Xinyuan-LilyGO/T-Halow/docs/EMC Authentication/泰芯AH模组-TX-AH-Rx00P 日本MIC证书&报告_20231007103027/MIC-RL-Certificate_230905005_219-239312.pdf

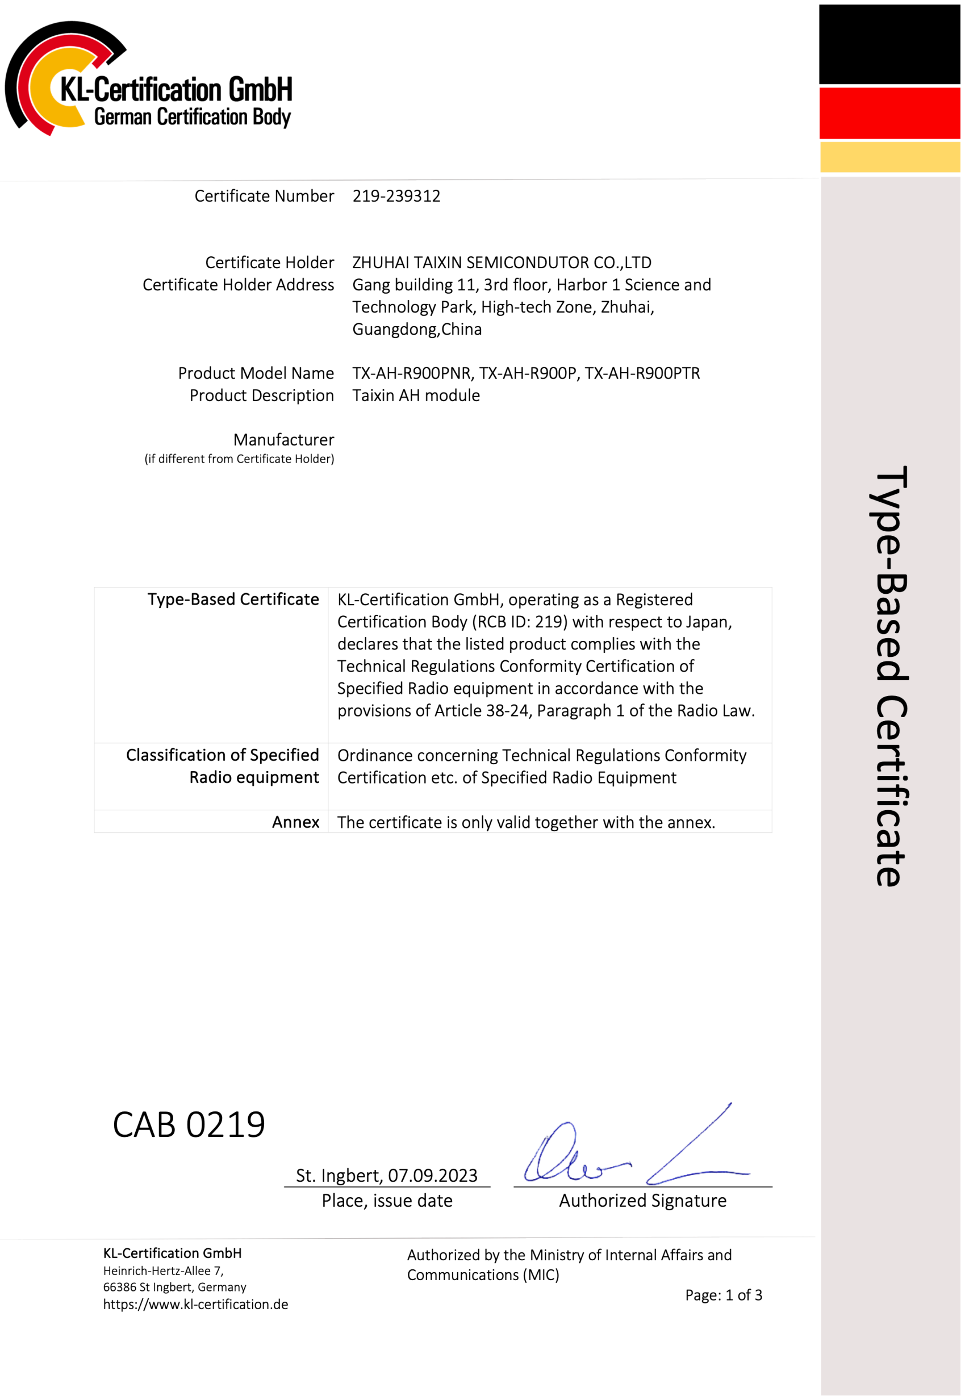
[picture p26: page 1]
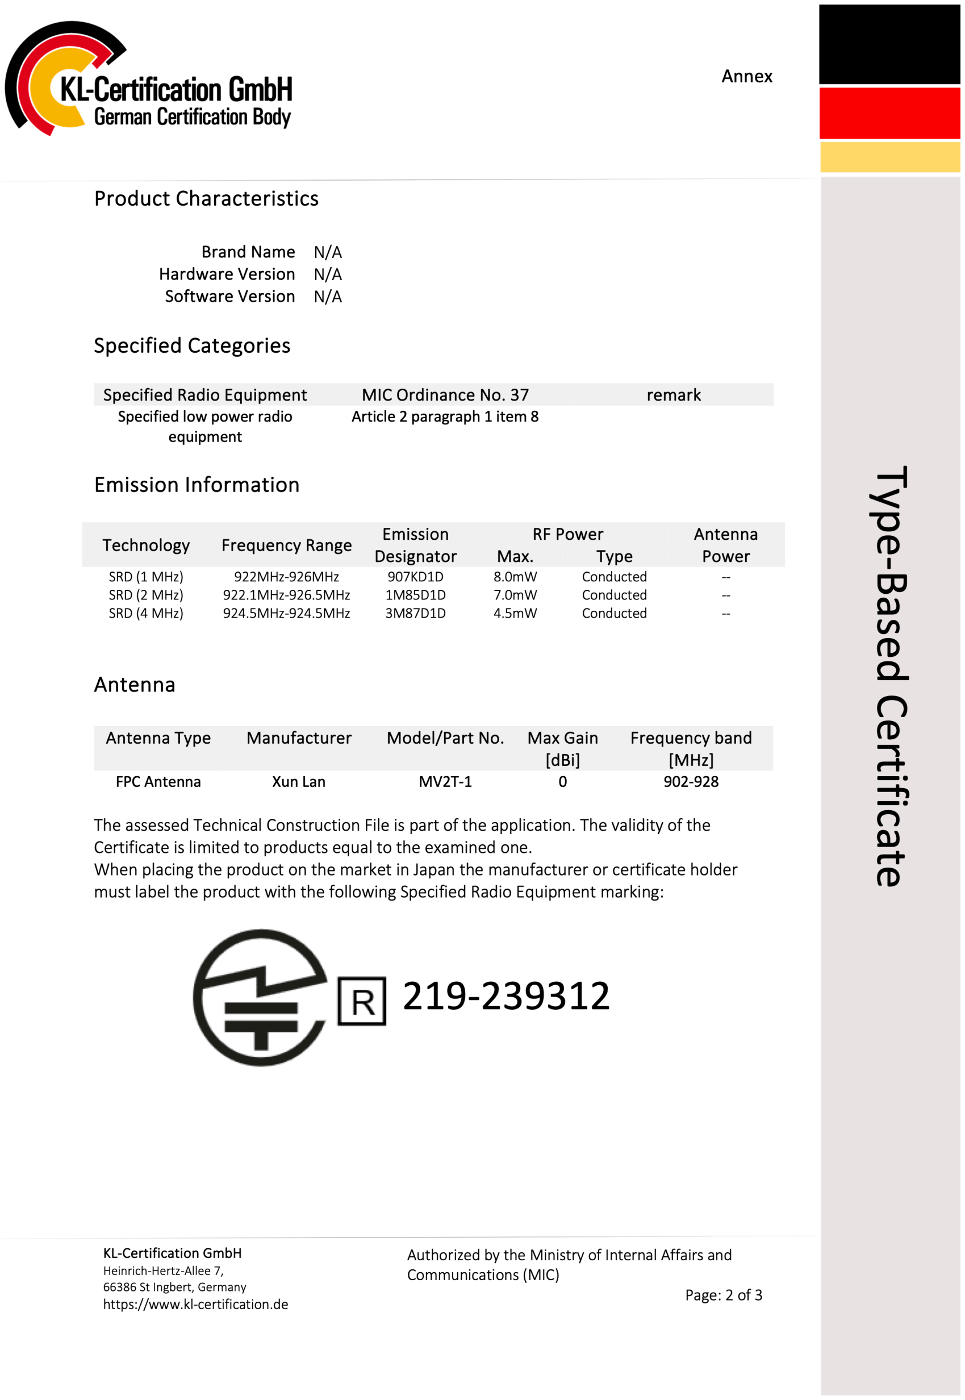
[picture p27: page 2]
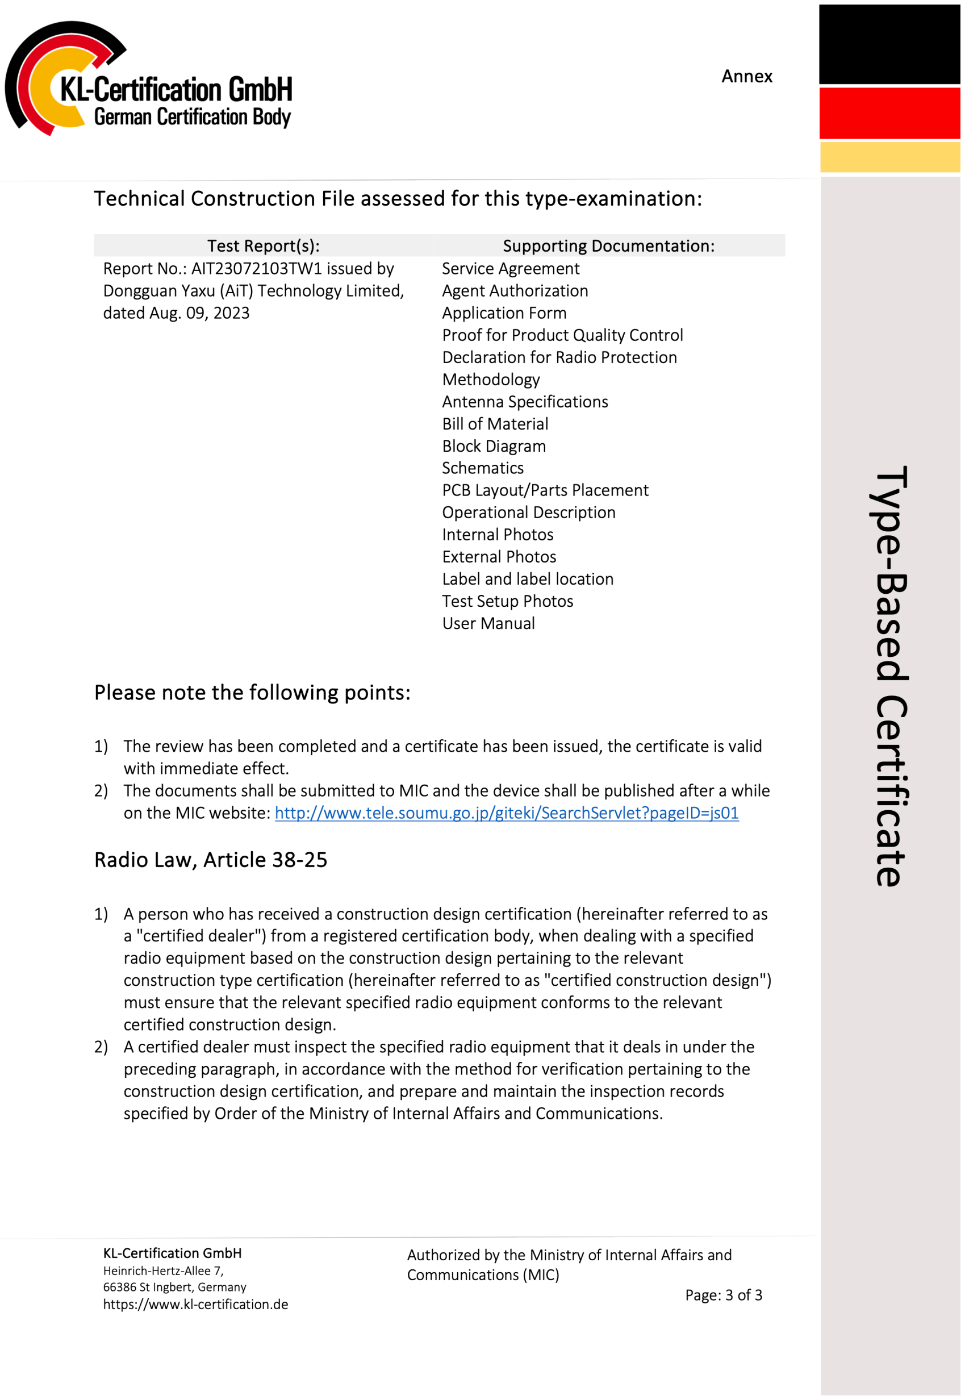
[picture p28: page 3]
