Xinyuan-LilyGO/T-Halow/docs/image/image-30.png

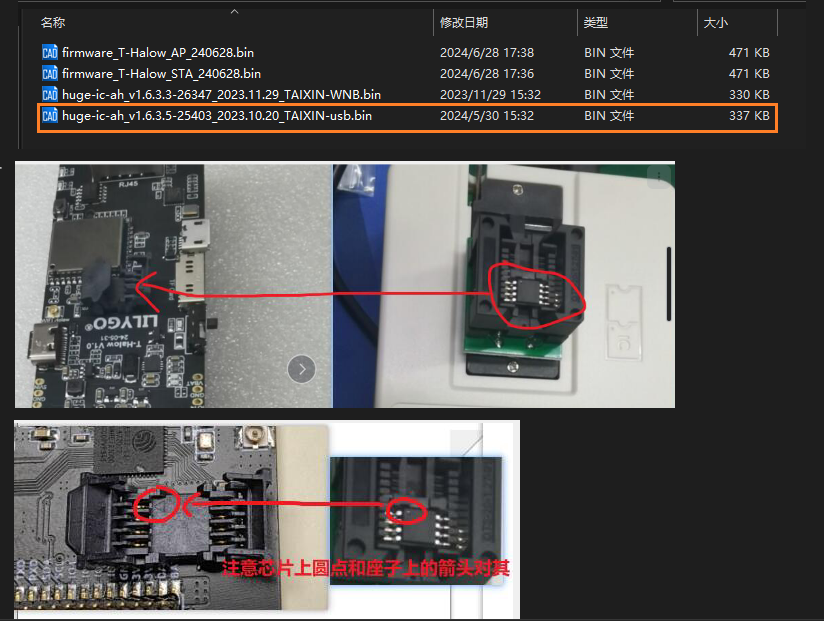
docs/image/image-30.png
