Xinyuan-LilyGO/T-Halow/docs/image/image-31.png

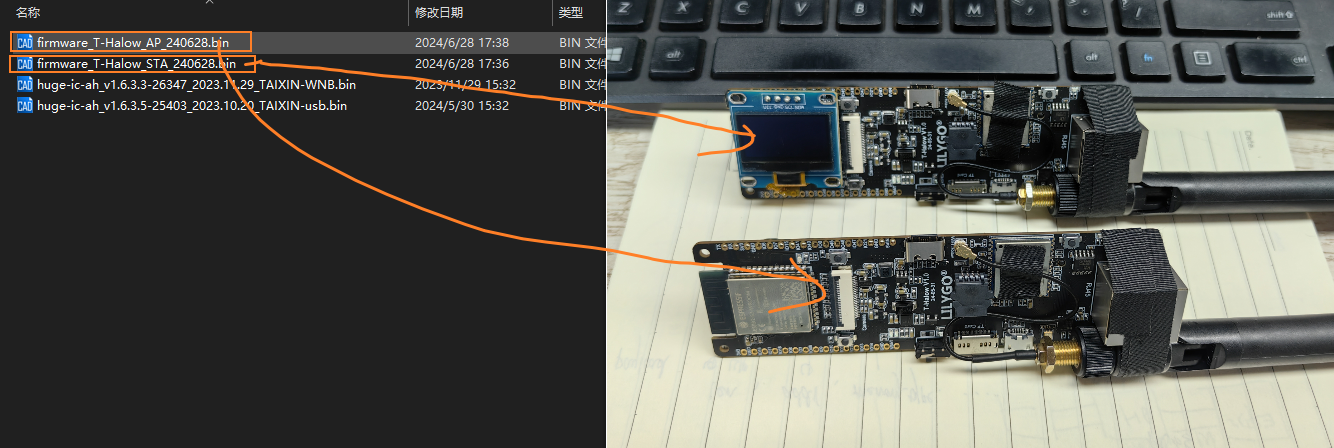
docs/image/image-31.png
