Xinyuan-LilyGO/T-Halow/docs/image/image-32.png

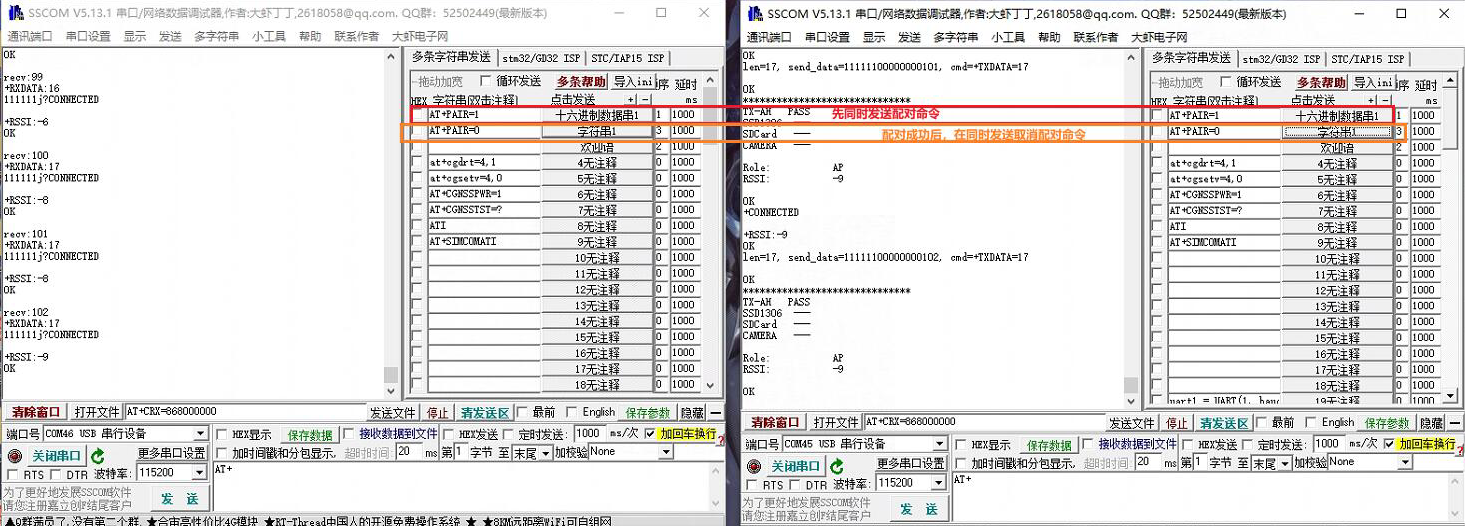
docs/image/image-32.png
