Xinyuan-LilyGO/T-Halow/docs/image/t_halow/VER1_front.jpg

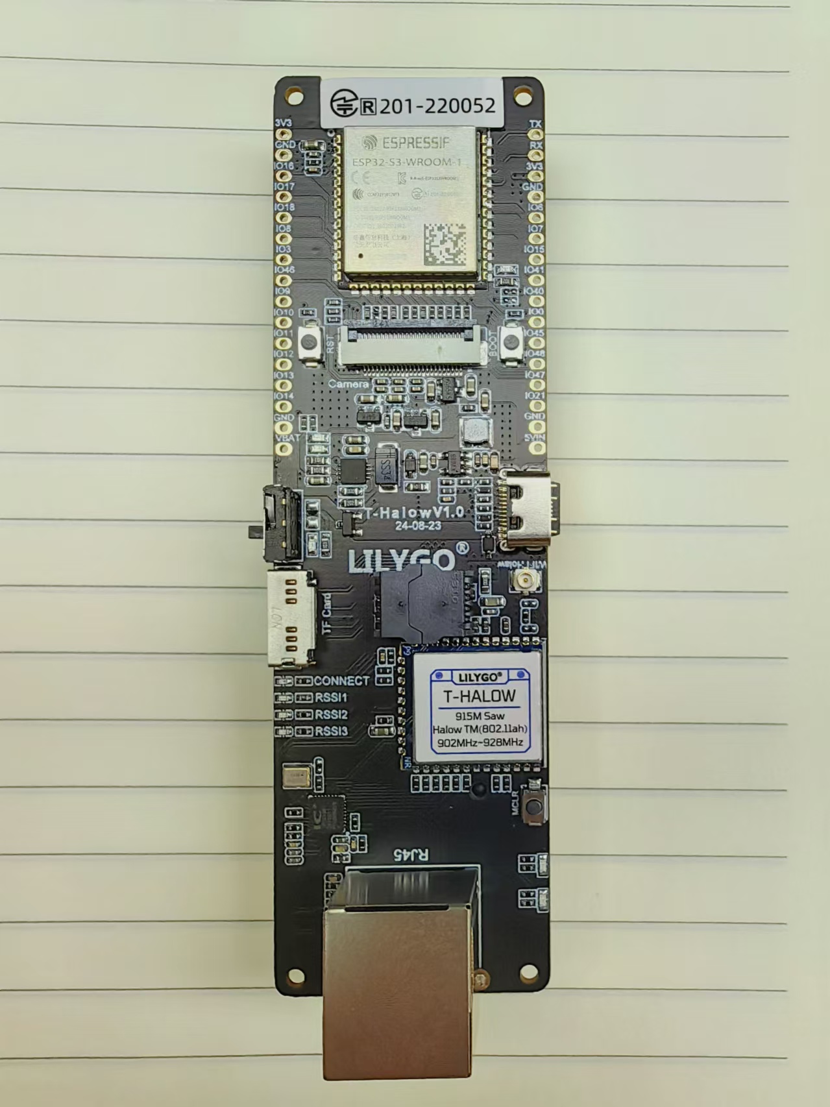
docs/image/t_halow/VER1_front.jpg
