Xinyuan-LilyGO/T-Halow/docs/image/t_halow/VER1_reverse.jpg

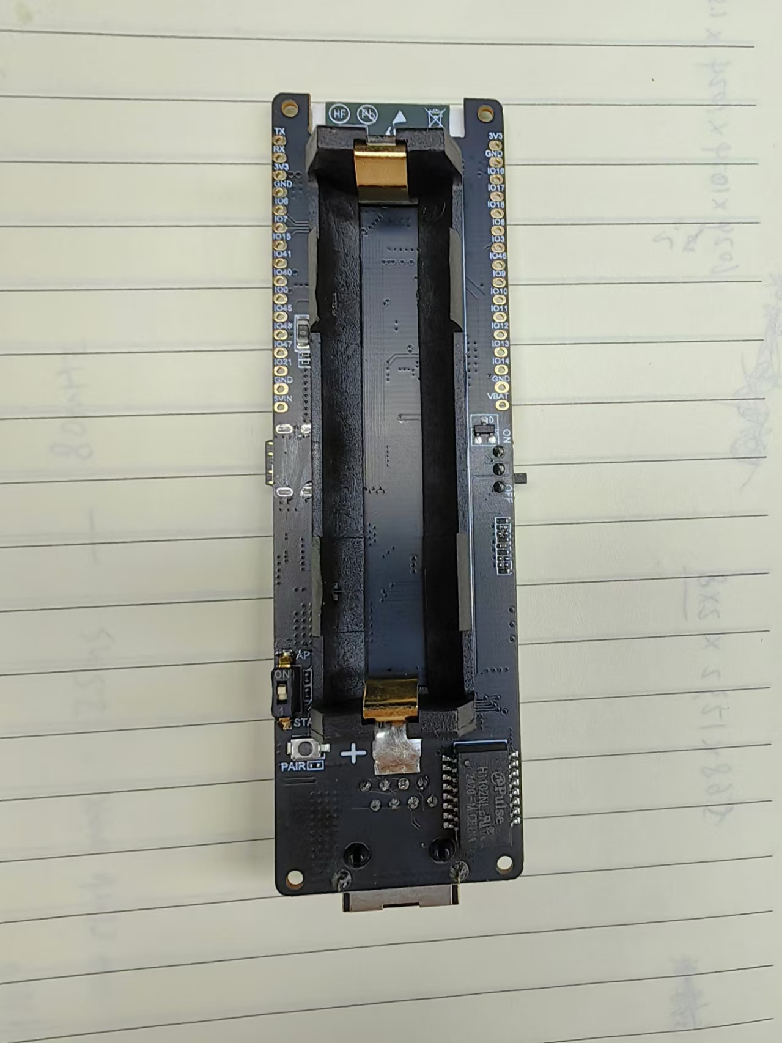
docs/image/t_halow/VER1_reverse.jpg
